scttnlsn/cell-monitor/src/balance.h

#ifndef __BALANCE_H__
#define __BALANCE_H__

#ifndef BALANCE_TIMEOUT
#define BALANCE_TIMEOUT 10000
#endif

class Balancer {
 public:
  Balancer(uint8_t pin);
  void enable();
  void disable();
  bool enabled();
  bool update();

 private:
  uint8_t _pin;
  uint8_t _enabled;
  uint32_t _enabled_time;
};

#endif
